3KUdelta/TapeCounter_Revox_B77/images/IMG_3231.jpg

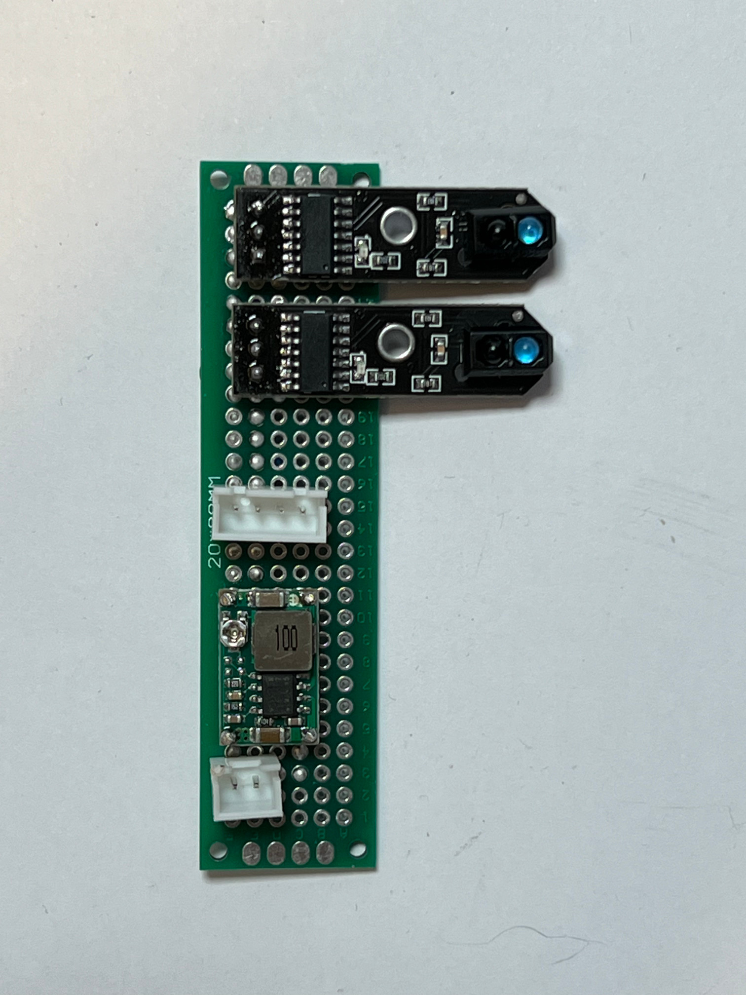
images/IMG_3231.jpg
